SpatialExperienceGroup/jotter/References/20160215_013727.jpg

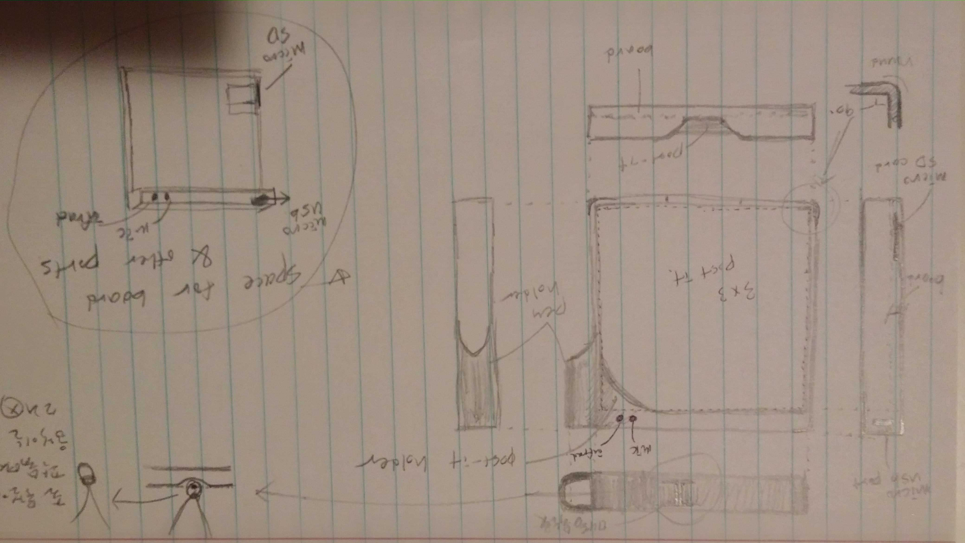
References/20160215_013727.jpg
