SpatialExperienceGroup/jotter/References/20160215_013743_HDR.jpg

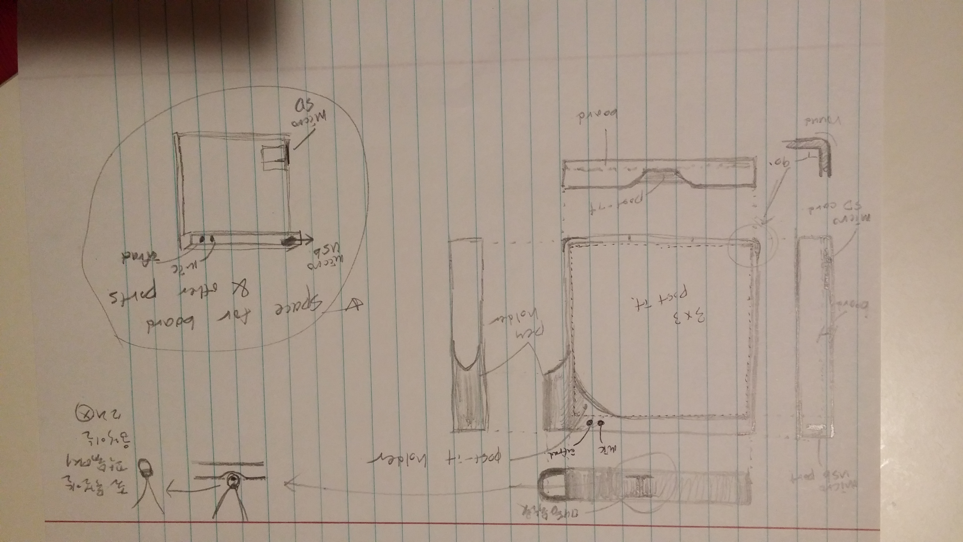
References/20160215_013743_HDR.jpg
