SpatialExperienceGroup/jotter/References/20160215_014230_HDR.jpg

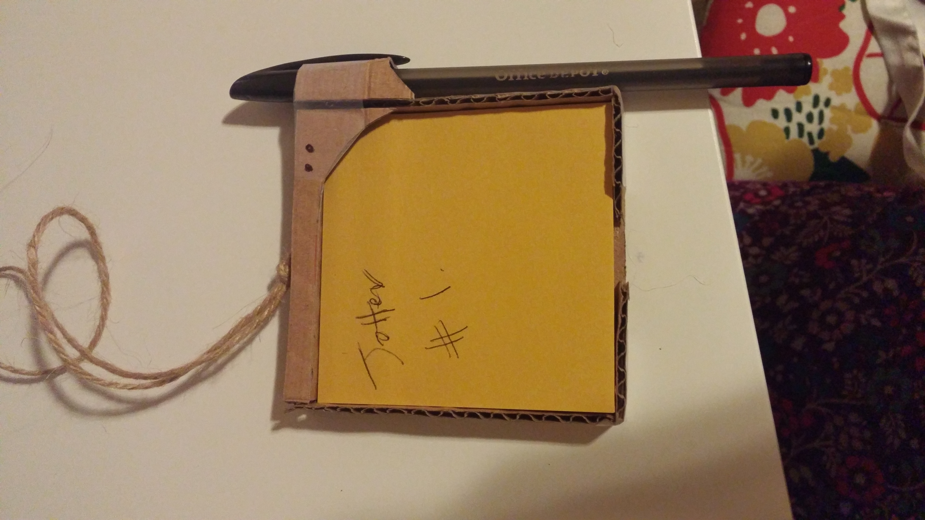
References/20160215_014230_HDR.jpg
