SpatialExperienceGroup/jotter/References/20160215_014244_HDR.jpg

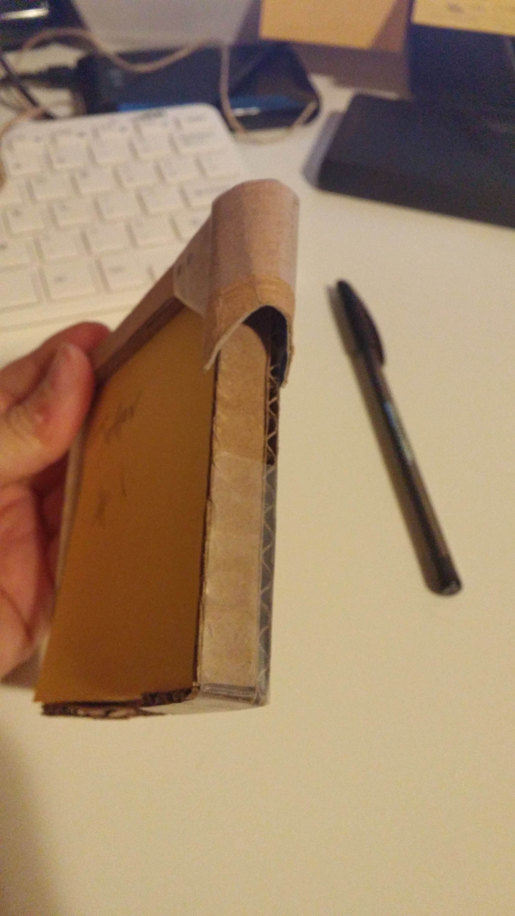
References/20160215_014244_HDR.jpg
