SpatialExperienceGroup/jotter/References/20160215_014342_HDR.jpg

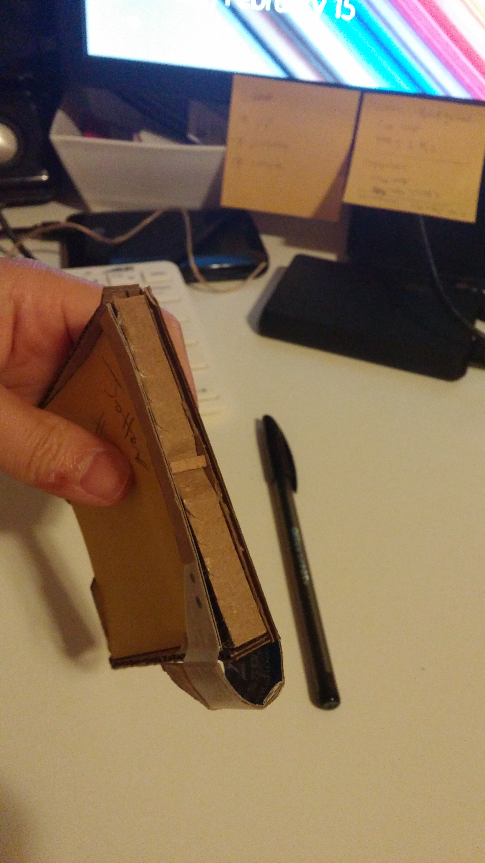
References/20160215_014342_HDR.jpg
