SpatialExperienceGroup/jotter/References/20160215_014353_HDR.jpg

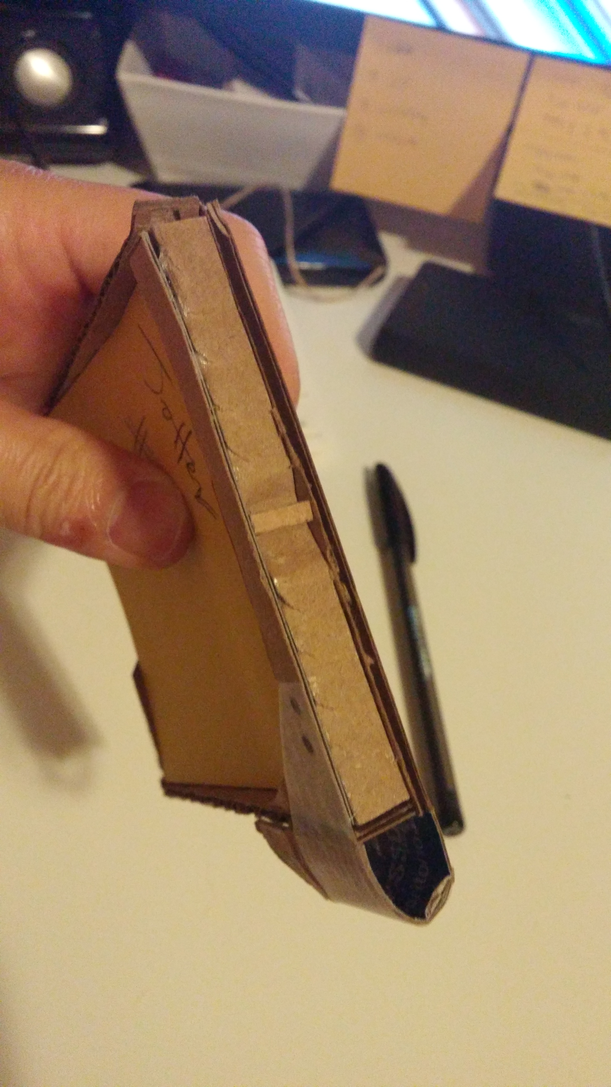
References/20160215_014353_HDR.jpg
