SpatialExperienceGroup/jotter/References/20160215_014411_HDR.jpg

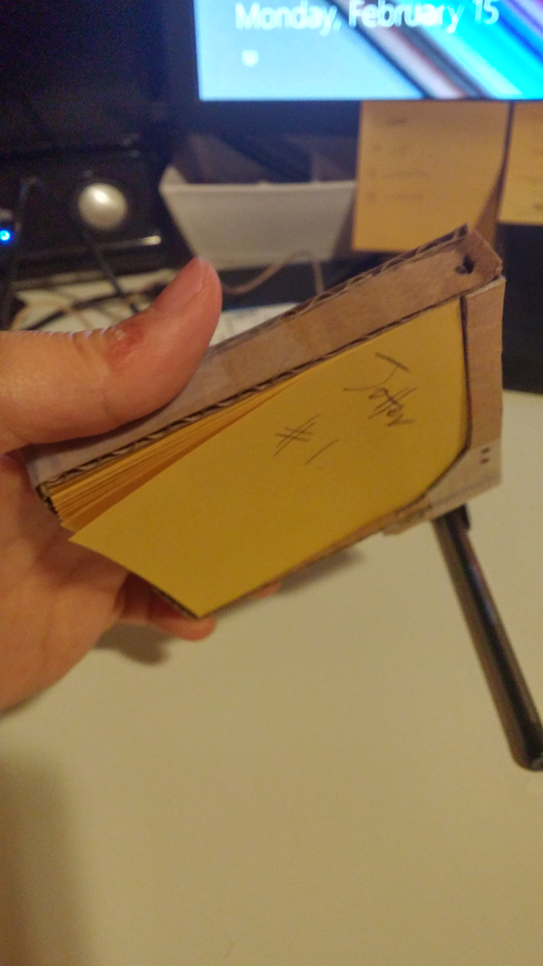
References/20160215_014411_HDR.jpg
