SpatialExperienceGroup/jotter/References/20160215_014505_HDR.jpg

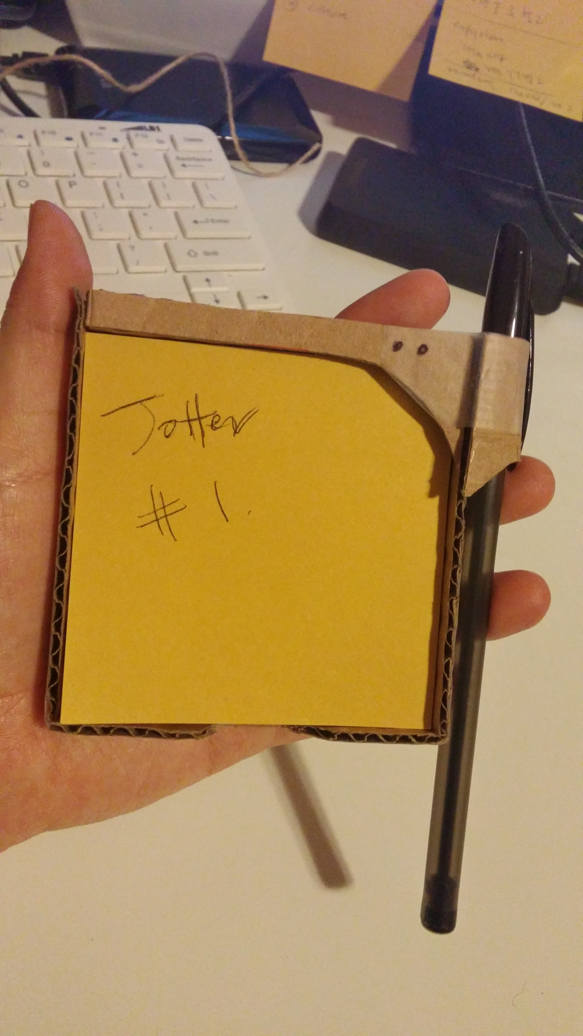
References/20160215_014505_HDR.jpg
